ElektroNeo/Adjustable-Wireless-Neuro-Stimulator-System/App/Bluetooth-1030x383.png

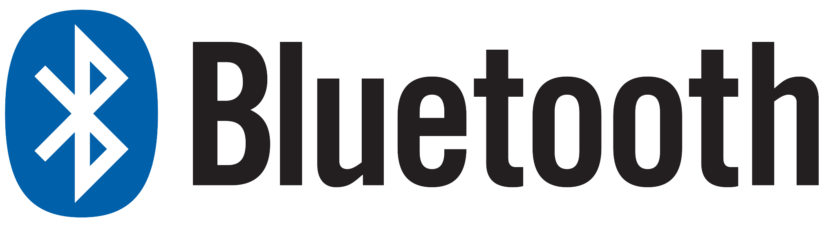
App/Bluetooth-1030x383.png
