ElektroNeo/Adjustable-Wireless-Neuro-Stimulator-System/App/pulse-description.png

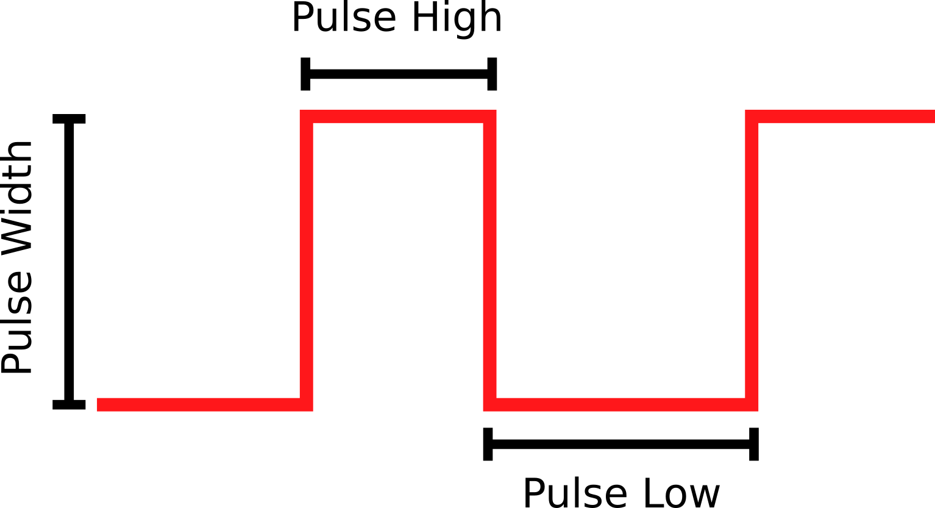
App/pulse-description.png
