ElektroNeo/Adjustable-Wireless-Neuro-Stimulator-System/Software/config.h

/* 
 * File:  config.h 
 * Author: Bahtiyar Bayram
 * Comments:
 * Revision history: v1.0
 */

// This is a guard condition so that contents of this file are not included
// more than once.  
#ifndef CONFIG_H
#define	CONFIG_H

#include <xc.h>
#include <stdint.h>
#include "dac.h"
#include "eusart.h"


// PIC16F1713 Configuration Bit Settings

// 'C' source line config statements

// CONFIG1
#pragma config FOSC = INTOSC    // Oscillator Selection Bits (INTOSC oscillator: I/O function on CLKIN pin)
#pragma config WDTE = OFF       // Watchdog Timer Enable (WDT disabled)
#pragma config PWRTE = OFF      // Power-up Timer Enable (PWRT disabled)
#pragma config MCLRE = ON       // MCLR Pin Function Select (MCLR/VPP pin function is MCLR)
#pragma config CP = OFF         // Flash Program Memory Code Protection (Program memory code protection is disabled)
#pragma config BOREN = OFF      // Brown-out Reset Enable (Brown-out Reset disabled)
#pragma config CLKOUTEN = OFF   // Clock Out Enable (CLKOUT function is disabled. I/O or oscillator function on the CLKOUT pin)
#pragma config IESO = OFF       // Internal/External Switchover Mode (Internal/External Switchover Mode is disabled)
#pragma config FCMEN = OFF      // Fail-Safe Clock Monitor Enable (Fail-Safe Clock Monitor is disabled)

// CONFIG2
#pragma config WRT = OFF        // Flash Memory Self-Write Protection (Write protection off)
#pragma config PPS1WAY = OFF    // Peripheral Pin Select one-way control (The PPSLOCK bit can be set and cleared repeatedly by software)
#pragma config ZCDDIS = ON      // Zero-cross detect disable (Zero-cross detect circuit is disabled at POR and can be enabled with ZCDSEN bit.)
#pragma config PLLEN = OFF      // Phase Lock Loop enable (4x PLL is enabled when software sets the SPLLEN bit)
#pragma config STVREN = OFF     // Stack Overflow/Underflow Reset Enable (Stack Overflow or Underflow will not cause a Reset)
#pragma config BORV = LO        // Brown-out Reset Voltage Selection (Brown-out Reset Voltage (Vbor), low trip point selected.)
#pragma config LPBOR = OFF      // Low-Power Brown Out Reset (Low-Power BOR is disabled)
#pragma config LVP = OFF         // Low-Voltage Programming Enable (Low-voltage programming enabled)

#define _XTAL_FREQ 16000000

#endif	/* CONFIG_H */
